facundoAlmon/esprc-brain/Imagenes/Auto/IMG_3515.jpg

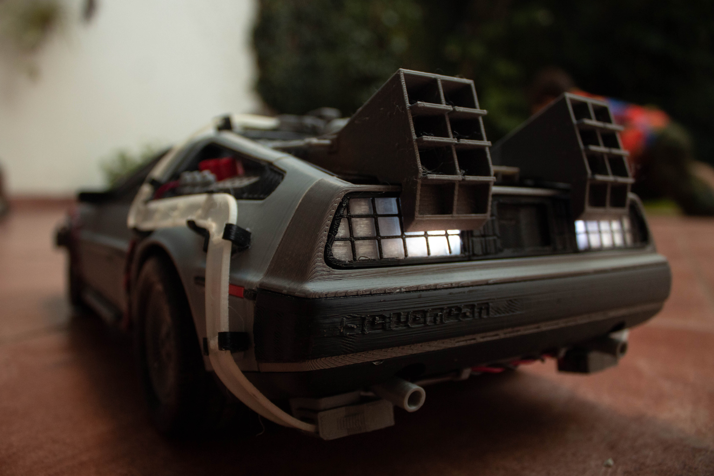
Imagenes/Auto/IMG_3515.jpg
