facundoAlmon/esprc-brain/Imagenes/Auto/IMG_184601440.jpg

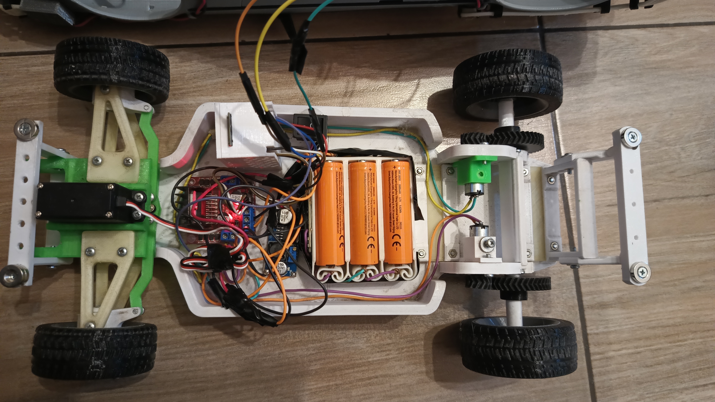
Imagenes/Auto/IMG_184601440.jpg
