facundoAlmon/esprc-brain/Imagenes/Webapp/en/01.png

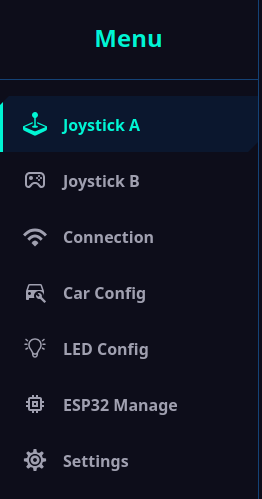
Imagenes/Webapp/en/01.png
