facundoAlmon/esprc-brain/Imagenes/Webapp/en/04.png

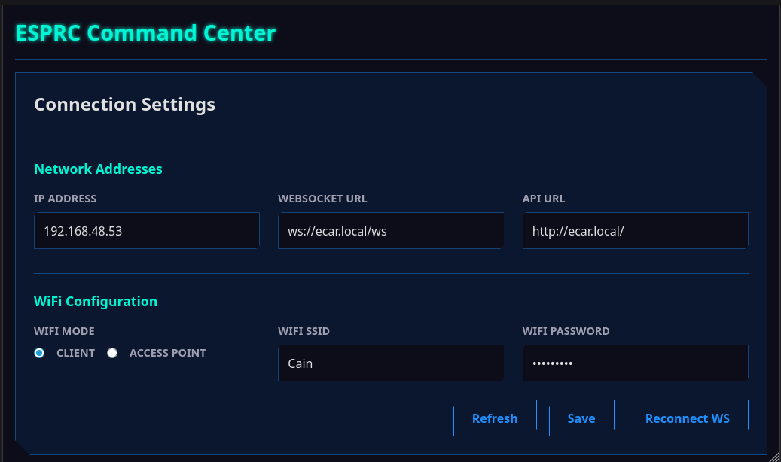
Imagenes/Webapp/en/04.png
