facundoAlmon/esprc-brain/Imagenes/Webapp/en/06.png

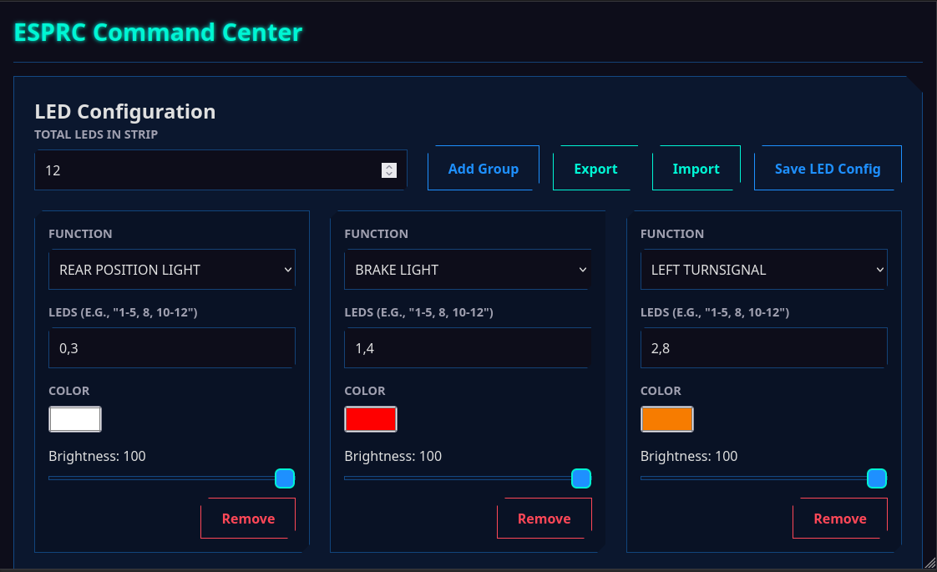
Imagenes/Webapp/en/06.png
