facundoAlmon/esprc-brain/Imagenes/Webapp/en/07.png

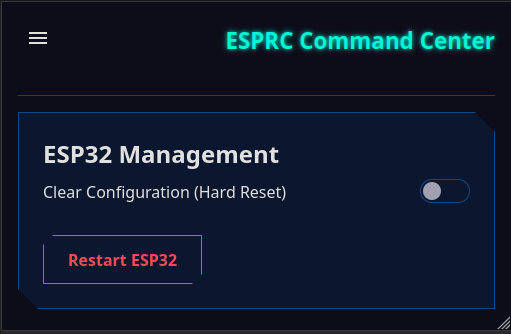
Imagenes/Webapp/en/07.png
