facundoAlmon/esprc-brain/Imagenes/Webapp/en/08.png

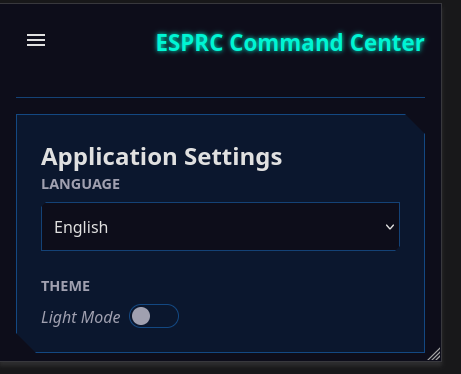
Imagenes/Webapp/en/08.png
