facundoAlmon/esprc-brain/Firmware/main/src/state.cpp

/**
 * @file state.cpp
 * @brief Implementación de funciones auxiliares relacionadas con el estado.
 * 
 * (Actualmente no hay implementaciones aquí, ya que las estructuras
 * de estado son manejadas directamente donde se utilizan).
 */
#include "state.h"
